Robert-Mones/Claculator/Claculator_Keypad/Imagery/sky2.png

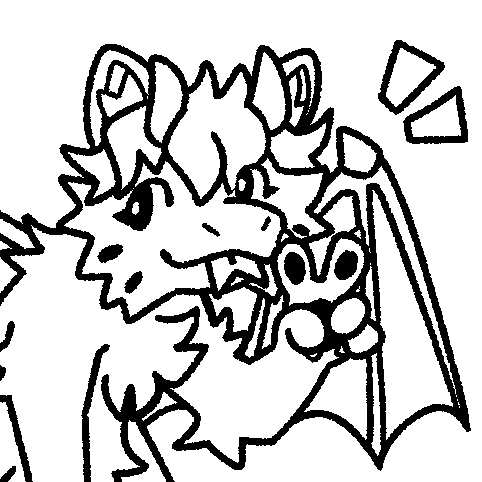
Claculator_Keypad/Imagery/sky2.png
