Robert-Mones/Claculator/Images/Assembled_1.jpg

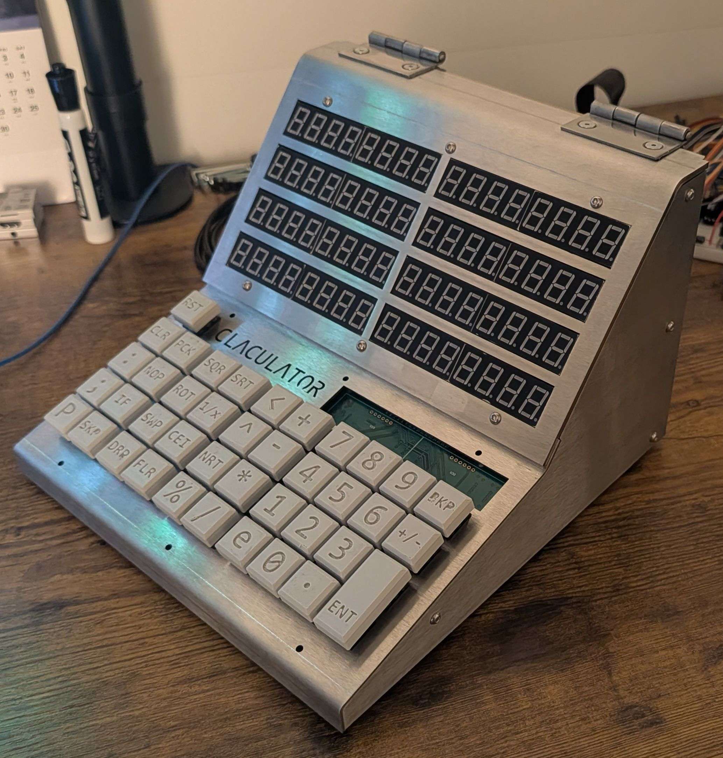
Images/Assembled_1.jpg
